jmoerschbach/ScoreDisplay/Code/MainDisplay/SevenSegmentVisualization.h

#ifndef _SEVENSEGMENTVISUALIZATION_h
#define _SEVENSEGMENTVISUALIZATION_h

#include <FastLED.h>
#include "Constants.h"
#include "SevenSegmentDigit.h"
#include "DataPackages.h"
#include "Utils.h"


#ifdef LED_DENSITY_LOW
constexpr int LEDS_PER_SEGMENT_TIME = 7;
constexpr int LEDS_PER_DOT = 2;
constexpr int LEDS_PER_SEGMENT_SCORE = 6;
constexpr int LEDS_PER_SEGMENT_HALFTIME = 4;
#else
constexpr int LEDS_PER_SEGMENT_TIME = 10;
constexpr int LEDS_PER_DOT = 3;
constexpr int LEDS_PER_SEGMENT_SCORE = 8;
constexpr int LEDS_PER_SEGMENT_HALFTIME = 5;
#endif

constexpr int NUMBER_DIGITS_TIME = 4;
constexpr int NUMBER_DIGITS_SCORE = 4;
constexpr int NUMBER_LEDS_TIME = 7 * LEDS_PER_SEGMENT_TIME * NUMBER_DIGITS_TIME + 2 * LEDS_PER_DOT;
constexpr int NUMBER_LEDS_SCORE = 7 * LEDS_PER_SEGMENT_SCORE * NUMBER_DIGITS_SCORE + 7 * LEDS_PER_SEGMENT_HALFTIME;
constexpr int DATA_PIN_LEDS_SCORE = A0;
constexpr int DATA_PIN_LEDS_TIME = A1;


class SevenSegmentVisualization {
public:
  void begin();
  void visualize(const MainDisplayData& data);
private:
  void updateTime(const MainDisplayData& data);
  void updateScoreAndHalftime(const MainDisplayData& data);
  void showTime(const MainDisplayData& data);
  void hideTime();

  SevenSegmentDigit _timeDigit_0 = SevenSegmentDigit(LEDS_PER_SEGMENT_TIME);
  SevenSegmentDigit _timeDigit_1 = SevenSegmentDigit(LEDS_PER_SEGMENT_TIME);
  SevenSegmentDigit _timeDigit_2 = SevenSegmentDigit(LEDS_PER_SEGMENT_TIME);
  SevenSegmentDigit _timeDigit_3 = SevenSegmentDigit(LEDS_PER_SEGMENT_TIME);

  SevenSegmentDigit _scoreHomeDigit_0 = SevenSegmentDigit(LEDS_PER_SEGMENT_SCORE, CRGB::Green);
  SevenSegmentDigit _scoreHomeDigit_1 = SevenSegmentDigit(LEDS_PER_SEGMENT_SCORE, CRGB::Green);
  SevenSegmentDigit _scoreAwayDigit_0 = SevenSegmentDigit(LEDS_PER_SEGMENT_SCORE, CRGB::Blue);
  SevenSegmentDigit _scoreAwayDigit_1 = SevenSegmentDigit(LEDS_PER_SEGMENT_SCORE, CRGB::Blue);
  SevenSegmentDigit _halftimeDigit = SevenSegmentDigit(LEDS_PER_SEGMENT_HALFTIME, CRGB::Red);

  CRGB _timeLeds[NUMBER_LEDS_TIME];
  CRGB _scoreLeds[NUMBER_LEDS_SCORE];
};
#endif
