jmoerschbach/ScoreDisplay/Code/MainDisplay/SevenSegmentDigit.cpp

#include "SevenSegmentDigit.h"

SevenSegmentDigit::SevenSegmentDigit(uint8_t ledsPerSegment, CRGB color) {
  _ledsPerSegment = ledsPerSegment;
  _color = color;
}

void SevenSegmentDigit::show(CRGB leds[], uint8_t value) {
  uint8_t digit = INVALID;
  if (value <= 9) {
    digit = DIGITS[value];
  }
  for (uint8_t segment = 0; segment < 7; segment++) {
    for (uint8_t j = 0; j < _ledsPerSegment; j++) {
      if (digit & (1 << segment)) {
        leds[segment * _ledsPerSegment + j] = _color;
      } else {
        leds[segment * _ledsPerSegment + j] = CRGB::Black;
      }
    }
  }
}

void SevenSegmentDigit::setColor(const CRGB& color) {
  _color = color;
}
